andrewperrindev/revxl/firmware/revxl/keymaps/vial/keymap.c

#include QMK_KEYBOARD_H

// Layer enum. _MAC = 0, _LOWER = 1, etc.
enum revxl_layers {
    _MAC,
    _LOWER,
    _RAISE,
    _ADJUST,
};

// Custom macro names.
enum custom_keycodes {
    GRD_SOLID = QK_KB_0,
    GRD_SPLSH,
    GRD_REACT,
    RBY_DBG
};

// Macro Bits.
bool process_record_user(uint16_t keycode, keyrecord_t *record) {
    switch (keycode) {
        // RGB Effect Shortcut: `gradient_left_right` (solid gradient)
        case GRD_SOLID:
            if (record->event.pressed) {
                rgb_matrix_mode(RGB_MATRIX_GRADIENT_LEFT_RIGHT);
            }
            return false;
        // RGB Effect Shortcut: `splash` (gradient reactive 'splashes')
        case GRD_SPLSH:
            if (record->event.pressed) {
                rgb_matrix_mode(RGB_MATRIX_SPLASH);
            }
            return false;
        // RGB Effect Shortcut: `solid_reactive_multinexus` (gradient reactive 'pulses')
        case GRD_REACT:
            if (record->event.pressed) {
                rgb_matrix_mode(RGB_MATRIX_SOLID_REACTIVE_MULTINEXUS);
            }
            return false;
        case RBY_DBG:
            if (record->event.pressed) {
                SEND_STRING("binding.pry");
            }
            return false;
        default:
            return true;

    }
}

static uint8_t original_effect = 0;

layer_state_t layer_state_set_user(layer_state_t state) {
    switch (get_highest_layer(state)) {
        case _RAISE:
            if (original_effect == 0) {
                original_effect = rgb_matrix_get_mode();
            }
            rgb_matrix_mode(RGB_MATRIX_CUSTOM_numpad_effect);
            break;
        default: // for any other layers, or the default layer
            if (original_effect != 0) {
                rgb_matrix_mode(original_effect);
                original_effect = 0;
            }
            break;
    }

    return state;
}

// OLED Bits.
#ifdef OLED_ENABLE

oled_rotation_t oled_init_user(oled_rotation_t rotation) { return OLED_ROTATION_180; }

bool oled_task_user(void) {
    // Layer 0 (Mac)
    static const char PROGMEM logo_mac[] = {
    0x00, 0x00, 0x00, 0x00, 0x00, 0xC0,
    0xF0, 0x7C, 0x1E, 0x0E, 0x0E, 0x1C,
    0x38, 0x70, 0xE0, 0xC0, 0xC0, 0xE0,
    0x70, 0x38, 0x1C, 0x0E, 0x0E, 0x1E,
    0x7C, 0xF0, 0xC0, 0x00, 0x00, 0x00,
    0x00, 0x00, 0x00, 0x00, 0x00, 0x00,
    0x00, 0xFC, 0xFC, 0xFC, 0xFC, 0xFC,
    0xFC, 0xFC, 0xFC, 0xFC, 0xFC, 0x7C,
    0x7C, 0x7C, 0x7C, 0x7C, 0x00, 0x00,
    0x00, 0xFC, 0xFC, 0xFC, 0xFC, 0xFC,
    0xFC, 0xFC, 0xFC, 0xFC, 0xFC, 0x7C,
    0x7C, 0x7C, 0x7C, 0x7C, 0x00, 0x00,
    0x00, 0xFC, 0xFC, 0xFC, 0xFC, 0xFC,
    0x00, 0x00, 0x00, 0x00, 0x00, 0xFC,
    0xFC, 0xFC, 0xFC, 0xFC, 0x00, 0x00,
    0x00, 0x7C, 0x7C, 0x7C, 0x7C, 0x7C,
    0x80, 0x80, 0x80, 0x80, 0x80, 0x7C,
    0x7C, 0x7C, 0x7C, 0x7C, 0x00, 0x00,
    0x00, 0xFC, 0xFC, 0xFC, 0xFC, 0xFC,
    0x00, 0x00, 0x00, 0x00, 0x00, 0x00,
    0x00, 0x00, 0x00, 0x00, 0x00, 0x00,
    0x00, 0x00, 0x00, 0xC0, 0xF0, 0x7C,
    0x1F, 0x07, 0x01, 0xF8, 0xF8, 0xF8,
    0xF8, 0xF8, 0xF8, 0xF8, 0xF8, 0x61,
    0x61, 0xF8, 0xF8, 0xF8, 0xF8, 0xF8,
    0xF8, 0xF8, 0xF8, 0x01, 0x07, 0x1F,
    0x7C, 0xF0, 0xC0, 0x00, 0x00, 0x00,
    0x00, 0x00, 0x00, 0xFF, 0xFF, 0xFF,
    0xFF, 0xFF, 0x0F, 0x0F, 0x0F, 0x0F,
    0x0F, 0xF0, 0xF0, 0xF0, 0xF0, 0xF0,
    0x00, 0x00, 0x00, 0xFF, 0xFF, 0xFF,
    0xFF, 0xFF, 0xFF, 0xFF, 0xFF, 0xFF,
    0xFF, 0xF0, 0xF0, 0xF0, 0xF0, 0xF0,
    0x00, 0x00, 0x00, 0x0F, 0x0F, 0x0F,
    0x0F, 0x0F, 0xF0, 0xF0, 0xF0, 0xF0,
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
    0x00, 0x00, 0x00, 0x0F, 0x0F, 0x0F,
    0x0F, 0x0F, 0xF0, 0xF0, 0xF0, 0xF0,
    0xF0, 0x0F, 0x0F, 0x0F, 0x0F, 0x0F,
    0x00, 0x00, 0x00, 0xF0, 0xF0, 0xF0,
    0xF0, 0xF0, 0x0F, 0x0F, 0x0F, 0x0F,
    0x0F, 0xF0, 0xF0, 0xF0, 0xF0, 0xF0,
    0x00, 0x00, 0x00, 0xFF, 0xFF, 0xFF,
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
    };

    // Layer 3
    static const char PROGMEM logo_adjust[] = {
    0x00, 0x00, 0x00, 0x00, 0x00, 0xC0,
    0xF0, 0x7C, 0x1E, 0x0E, 0x0E, 0x1C,
    0x38, 0x70, 0xE0, 0xC0, 0xC0, 0xE0,
    0x70, 0x38, 0x1C, 0x0E, 0x0E, 0x1E,
    0x7C, 0xF0, 0xC0, 0x00, 0x00, 0x00,
    0x00, 0x00, 0x00, 0x00, 0x00, 0x00,
    0x00, 0xFC, 0xFC, 0xFC, 0xFC, 0xFC,
    0xFC, 0xFC, 0xFC, 0xFC, 0xFC, 0x7C,
    0x7C, 0x7C, 0x7C, 0x7C, 0x00, 0x00,
    0x00, 0xFC, 0xFC, 0xFC, 0xFC, 0xFC,
    0xFC, 0xFC, 0xFC, 0xFC, 0xFC, 0x7C,
    0x7C, 0x7C, 0x7C, 0x7C, 0x00, 0x00,
    0x00, 0xFC, 0xFC, 0xFC, 0xFC, 0xFC,
    0x00, 0x00, 0x00, 0x00, 0x00, 0xFC,
    0xFC, 0xFC, 0xFC, 0xFC, 0x00, 0x00,
    0x00, 0x7C, 0x7C, 0x7C, 0x7C, 0x7C,
    0x80, 0x80, 0x80, 0x80, 0x80, 0x7C,
    0x7C, 0x7C, 0x7C, 0x7C, 0x00, 0x00,
    0x00, 0xFC, 0xFC, 0xFC, 0xFC, 0xFC,
    0x00, 0x00, 0x00, 0x00, 0x00, 0x00,
    0x00, 0x00, 0x00, 0x00, 0x00, 0x00,
    0x00, 0x00, 0x00, 0xC0, 0xF0, 0x7C,
    0x1F, 0x07, 0x01, 0xF8, 0xF8, 0xF8,
    0xF8, 0xF8, 0xF8, 0xF8, 0xF8, 0x61,
    0x61, 0xF8, 0xF8, 0xF8, 0xF8, 0xF8,
    0xF8, 0xF8, 0xF8, 0x01, 0x07, 0x1F,
    0x7C, 0xF0, 0xC0, 0x00, 0x00, 0x00,
    0x00, 0x00, 0x00, 0xFF, 0xFF, 0xFF,
    0xFF, 0xFF, 0x0F, 0x0F, 0x0F, 0x0F,
    0x0F, 0xF0, 0xF0, 0xF0, 0xF0, 0xF0,
    0x00, 0x00, 0x00, 0xFF, 0xFF, 0xFF,
    0xFF, 0xFF, 0xFF, 0xFF, 0xFF, 0xFF,
    0xFF, 0xF0, 0xF0, 0xF0, 0xF0, 0xF0,
    0x00, 0x00, 0x00, 0x0F, 0x0F, 0x0F,
    0x0F, 0x0F, 0xF0, 0xF0, 0xF0, 0xF0,
    0xF0, 0x0F, 0x0F, 0x0F, 0x0F, 0x0F,
    0x00, 0x00, 0x00, 0xF0, 0xF0, 0xF0,
    0xF0, 0xF0, 0x0F, 0x0F, 0x0F, 0x0F,
    0x0F, 0xF0, 0xF0, 0xF0, 0xF0, 0xF0,
    0x00, 0x00, 0x00, 0xFF, 0xFF, 0xFF,
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
    };

    // Function to swap the images out based on which layer is being shown.
    switch (get_highest_layer(layer_state)) {
        case _MAC:
            if (keymap_config.swap_lctl_lgui) { oled_write_raw_P(logo_win, sizeof(logo_win)); }
            else { oled_write_raw_P(logo_mac, sizeof(logo_mac)); }
            break;
        case _LOWER:
            oled_write_raw_P(logo_lower, sizeof(logo_lower));
            break;
        case _RAISE:
            oled_write_raw_P(logo_raise, sizeof(logo_raise));
            break;
        case _ADJUST:
            oled_write_raw_P(logo_adjust, sizeof(logo_adjust));
            break;
        default:
            // Or use the write_ln shortcut over adding '\n' to the end of your string
            oled_write_ln_P(PSTR("Undefined"), false);
    }

    return false;
}
#endif

// The Keymap
const uint16_t PROGMEM keymaps[][MATRIX_ROWS][MATRIX_COLS] = {
    // Base Mac Layout
    // ,-----------------------------------------.          ,-----------------------------------------. ,--------------------.
    // |  `   |  1   |  2   |  3   |  4   |  5   |          |  6   |  7   |  8   |  9   |  0   |  -   | |  Ins | Home | PgUp |
    // |------+------+------+------+------+------|          |------+------+------+------+------+------| |------+------+------|
    // | Esc  |  Q   |  W   |  E   |  R   |  T   |          |  Y   |  U   |  I   |  O   |  P   | BSPC | |  Del | End  | PgDn |
    // |------+------+------+------+------+------|          |------+------+------+------+------+------| '--------------------'
    // | Tab  |  A   |  S   |  D   |  F   |  G   |          |  H   |  J   |  K   |  L   |  ;   |  '   |
    // |------+------+------+------+------+------|          |------+------+------+------+------+------|        ,------.
    // | Shift|  Z   |  X   |  C   |  V   |  B   |          |  N   |  M   |  ,   |  .   |  /   | Shift|        | Up   |
    // `-------------+------+------+------+------| ,------. |------+------+------+------+------+------' ,------+------+------.
    //        | Ctrl | Alt  | Cmd  | Lower| Enter| | Mute | | Space| Raise| Cmd  | Alt  | Ctrl |        | Left | Down | Right|
    //        `----------------------------------' `------' '----------------------------------'        '--------------------'
    //
    [_MAC] = LAYOUT(
        KC_GRV,  KC_1,    KC_2,    KC_3,    KC_4,  KC_5,               KC_6,   KC_7,  KC_8,    KC_9,    KC_0,    KC_MINS,         KC_INS,  KC_HOME, KC_PGUP,
        KC_ESC,  KC_Q,    KC_W,    KC_E,    KC_R,  KC_T,               KC_Y,   KC_U,  KC_I,    KC_O,    KC_P,    KC_BSPC,         KC_DEL,  KC_END,  KC_PGDN,
        KC_TAB,  KC_A,    KC_S,    KC_D,    KC_F,  KC_G,               KC_H,   KC_J,  KC_K,    KC_L,    KC_SCLN, KC_QUOT,
        KC_LSFT, KC_Z,    KC_X,    KC_C,    KC_V,  KC_B,               KC_N,   KC_M,  KC_COMM, KC_DOT,  KC_SLSH, RSFT_T(KC_ENT),                   KC_UP,
                 KC_LCTL, KC_LALT, KC_LGUI, MO(_LOWER), KC_ENT, KC_MUTE, KC_SPC, TT(_RAISE), KC_RGUI, KC_RALT, RCTL_T(KC_CAPS),          KC_LEFT, KC_DOWN, KC_RIGHT
    ),
    // Lower Layout
    // ,-----------------------------------------.          ,-----------------------------------------. ,--------------------.
    // |      |  F1  |  F2  |  F3  |  F4  |  F5  |          |  F6  |  F7  |  F8  |  F9  |  F10 |   =  | |RBY_DG|Gui+L |      |
    // |------+------+------+------+------+------|          |------+------+------+------+------+------| |------+------+------|
    // |      | F11  | F12  |  3   |  4   |  5   |          |  6   |  7   |  8   |  9   |  [   |   ]  | |      |Gui+R |      |
    // |------+------+------+------+------+------|          |------+------+------+------+------+------| '--------------------'
    // |      |  !   |  @   |  #   |  $   |  %   |          |  ^   |  &   |  *   |  (   |  )   |  |   |
    // |------+------+------+------+------+------|          |------+------+------+------+------+------|        ,------.
    // |      |  =   |  -   |  +   |  {   |  }   |          |  [   |  ]   |  ;   |  :   |  \   |      |        |      |
    // `-------------+------+------+------+------| ,------. |------+------+------+------+------+------' ,------+------+------.
    //        |      |      |      |      |      | | Play | |      | Raise|      |      |      |        |      |      |      |
    //        `----------------------------------' `------' '----------------------------------'        '--------------------'
    //
    [_LOWER] = LAYOUT(
        _______,  KC_F1,   KC_F2,   KC_F3,   KC_F4,   KC_F5,               KC_F6,   KC_F7,   KC_F8,   KC_F9,   KC_F10,   KC_EQL,  RBY_DBG, LGUI(KC_LEFT),  _______,
        _______,  KC_F11,  KC_F12,    KC_3,    KC_4,    KC_5,                KC_6,    KC_7,    KC_8,    KC_9,  KC_LBRC, KC_RBRC,  _______, LGUI(KC_RIGHT), _______,
        _______,  KC_EXLM, KC_AT,   KC_HASH, KC_DLR,  KC_PERC,             KC_CIRC, KC_AMPR, KC_ASTR, KC_LPRN, KC_RPRN, KC_PIPE,
        _______,  KC_EQL,  KC_MINS, KC_PLUS, KC_LCBR, KC_RCBR,             KC_LBRC, KC_RBRC, KC_SCLN, KC_COLN, KC_BSLS, _______,                _______,
                  _______, _______, _______, _______, _______,   KC_MPLY,  _______, MO(_ADJUST),   _______, _______, _______,          _______, _______, _______
    ),
    // Upper Layout
    // ,-----------------------------------------.          ,-----------------------------------------. ,--------------------.
    // |      |      |      |      |      |      |          |      |  7   |  8   |  9   |      |      | |      |Ctl+A |      |
    // |------+------+------+------+------+------|          |------+------+------+------+------+------| |------+------+------|
    // |      |      | Up   |      |      |      |          |      |  4   |  5   |  6   |      |      | |      |Ctl+E |      |
    // |------+------+------+------+------+------|          |------+------+------+------+------+------| '--------------------'
    // |      | Left | Down |Right |      | CapsL|          |      |  1   |  2   |  3   |      |      |
    // |------+------+------+------+------+------| ,------. |------+------+------+------+------+------|        ,------.
    // |      |      |      |      |      |      | | Play | |      |  0   |  .   |Enter |      |      |        |      |
    // `-------------+------+------+------+------| `------' |------+------+------+------+------+------' ,------+------+------.
    //        |      |      |      | Lower|      |          |      |      |      |      |      |        |      |      |      |
    //        `----------------------------------'          '----------------------------------'        '--------------------'
    //
    [_RAISE] = LAYOUT(
        _______,  _______,  _______,  _______,  _______,  _______,             _______,  KC_P7,    KC_P8,    KC_P9,  _______,  _______,    _______,  LCTL(KC_A),  _______,
        _______,  _______,  KC_UP,    _______,  _______,  _______,             _______,  KC_P4,    KC_P5,    KC_P6,  _______,  _______,    _______,  LCTL(KC_E),  _______,
        _______,  KC_LEFT,  KC_DOWN,  KC_RIGHT, _______,  KC_CAPS,             _______,  KC_P1,    KC_P2,    KC_P3,  _______,  _______,
        _______,  _______,  _______,  _______,  _______,  _______,             _______,  KC_P0,  KC_PDOT,  KC_PENT,  _______,  _______,            _______,
                  _______,  _______,  _______,  MO(_ADJUST),  _______,   KC_MPLY,  _______,  _______,  _______,  _______,  _______,            _______,  _______,  _______
    ),
    // Adjust Layout
    // ,-----------------------------------------.          ,-----------------------------------------. ,--------------------.
    // | RGB  | Solid|Splash|      |      |      |          |      |      |      |      |      |      | |      |      |      |
    // |------+------+------+------+------+------|          |------+------+------+------+------+------| |------+------+------|
    // | RGB  | Spd+ | Val+ | Sat+ | Hue+ | Mode+|          |      |      |      |      |      |      | |      |      |      |
    // |------+------+------+------+------+------|          |------+------+------+------+------+------| '--------------------'
    // |MacWin| Spd- | Val- | Sat- | Hue- | Mode-|          |      | VolDn| Mute | VolUp|      |      |
    // |------+------+------+------+------+------| ,------. |------+------+------+------+------+------|        ,------.
    // |      |      |      |      |      |      | | Play | |      | Prev | Play | Next |      |      |        |      |
    // `-------------+------+------+------+------| `------' |------+------+------+------+------+------' ,------+------+------.
    //        |      |      |      |      |      |          |      |      |      |      |      |        | Mode-|      | Mode+|
    //        `----------------------------------'          '----------------------------------'        '--------------------'
    //
    [_ADJUST] = LAYOUT(
        RGB_TOG,GRD_SOLID,GRD_SPLSH,GRD_REACT,  _______,  _______,             _______,  _______,  _______,  _______,  _______,  _______,  _______,  _______,  _______,
        RGB_TOG,  RGB_SPI,  RGB_VAI,  RGB_SAI,  RGB_HUI,  RGB_MODE_FORWARD,    _______,  _______,  _______,  _______,  _______,  _______,  _______,  _______,  _______,
        CG_TOGG,  RGB_SPD,  RGB_VAD,  RGB_SAD,  RGB_HUD,  RGB_MODE_REVERSE,    _______,  KC_VOLD,  KC_MUTE,  KC_VOLU,  _______,  _______,
        _______,  _______,  _______,  _______,  _______,  _______,             _______,  KC_MPRV,  KC_MPLY,  KC_MNXT,  _______,  _______,                     _______,
                  _______,  _______,  _______,  _______,  _______,   KC_MPLY,  _______,  _______,  _______,  _______,  _______,            RGB_MODE_REVERSE,  _______,  RGB_MODE_FORWARD
    )
};

// Encoder Definition.
#if defined(ENCODER_MAP_ENABLE)
const uint16_t PROGMEM encoder_map[][NUM_ENCODERS][NUM_DIRECTIONS] = {
    [_MAC] = { ENCODER_CCW_CW(KC_VOLD, KC_VOLU) },
    [_LOWER] = { ENCODER_CCW_CW(KC_MPRV, KC_MNXT) },
    [_RAISE] = { ENCODER_CCW_CW(KC_MPRV, KC_MNXT) },
    [_ADJUST] = { ENCODER_CCW_CW(RGB_MODE_REVERSE, RGB_MODE_FORWARD) }
};
#endif
